yiakonale/high-speed-photography-v1/rev1/pcb-kicad/boost/Boost_Converter_PCB/boost_converter_placement.GIF

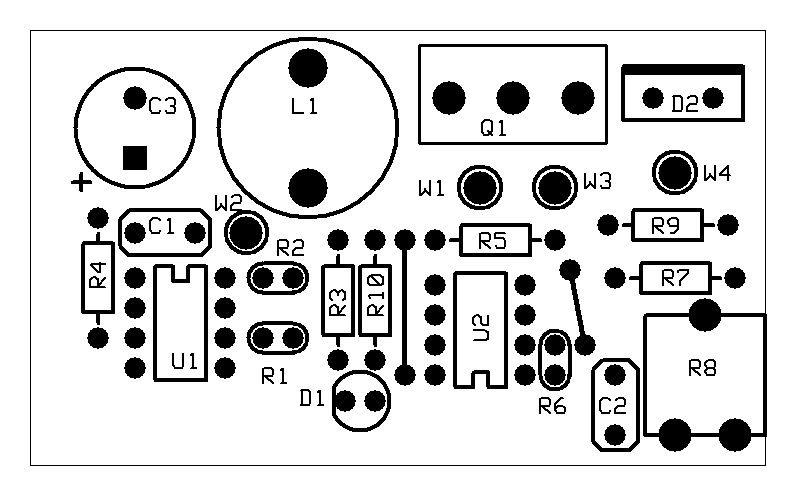
rev1/pcb-kicad/boost/Boost_Converter_PCB/boost_converter_placement.GIF
