yiakonale/high-speed-photography-v1/rev1/boost-sim.asc

C1: cap; 100µ; Rser=0.13
D1: diode; MUR460
L1: ind; 100µ; Rser=0.042
M1: nmos; SPA11N60C3
V1: voltage; 12
V2: voltage; PULSE(0 12 0 0 0 50u 100u)
Named nets: 0
.tran 0 5 0 0.1
